Bastelschlumpf/SolarSystemOffGrid/mqqtbridge/circuit/WemosESP32.png

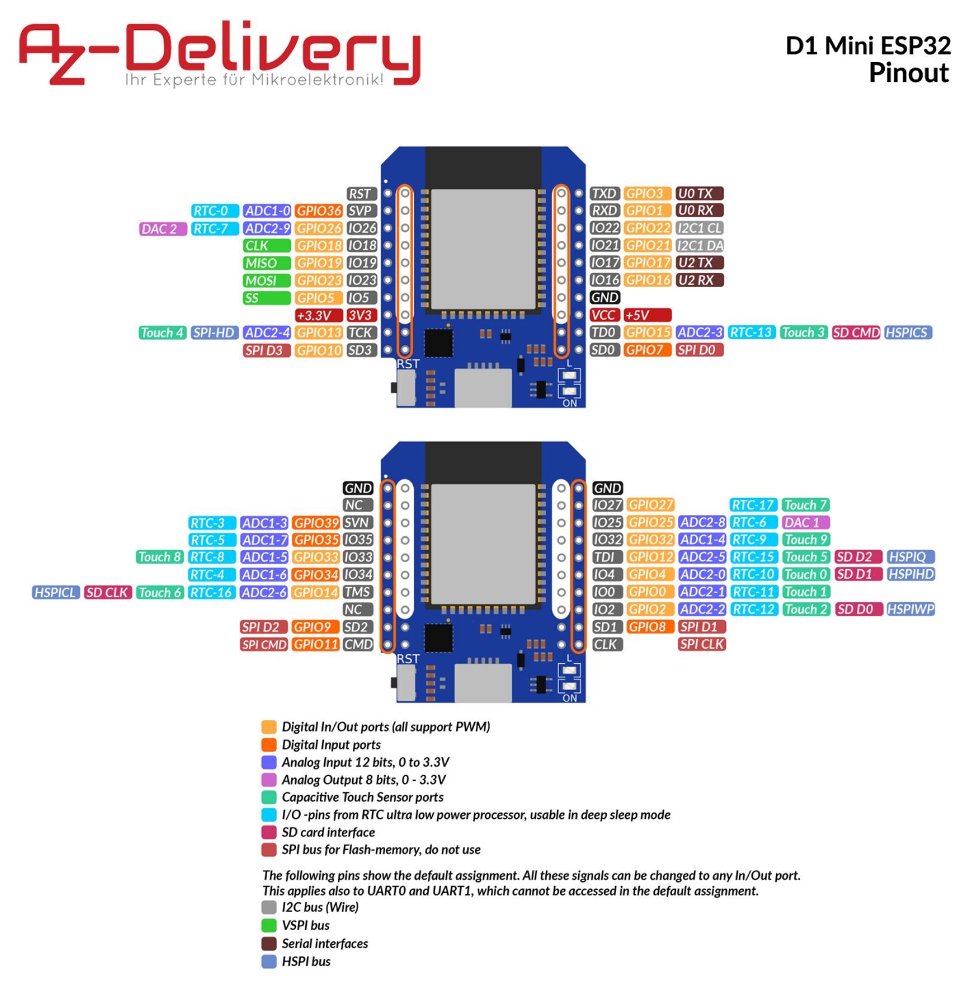
mqqtbridge/circuit/WemosESP32.png
